kiu/lofence/pics/lofence_grafana_details.png

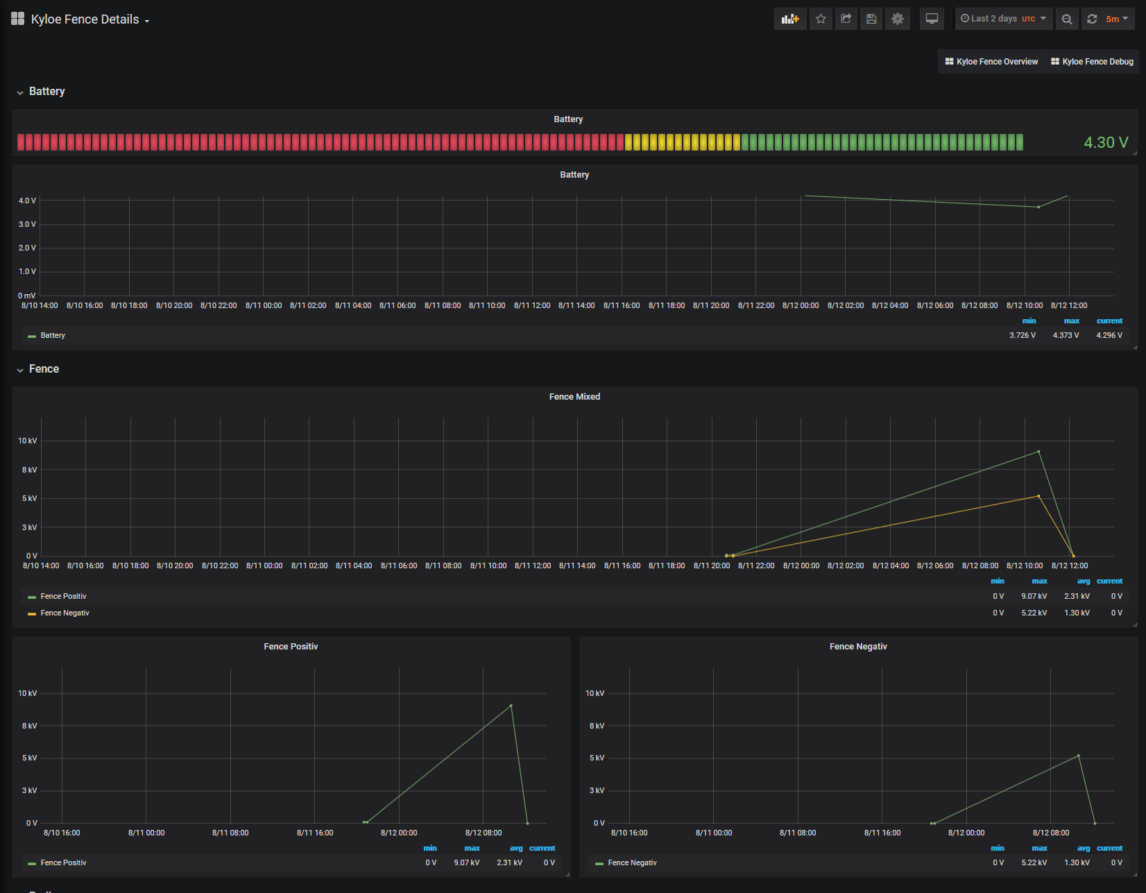
pics/lofence_grafana_details.png
