kiu/lofence/pics/lofence_rfm95_proto.jpg

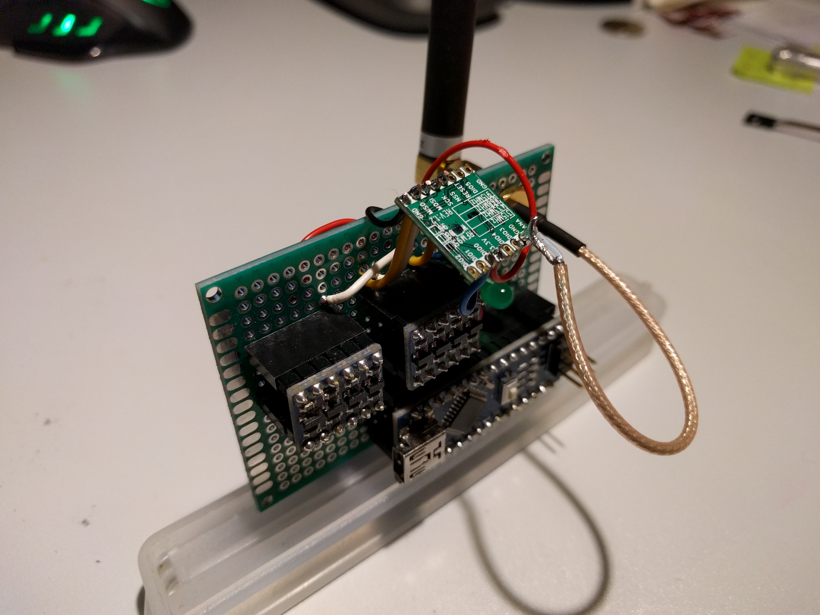
pics/lofence_rfm95_proto.jpg
