kiu/lofence/pics/lofence_ttig.jpg

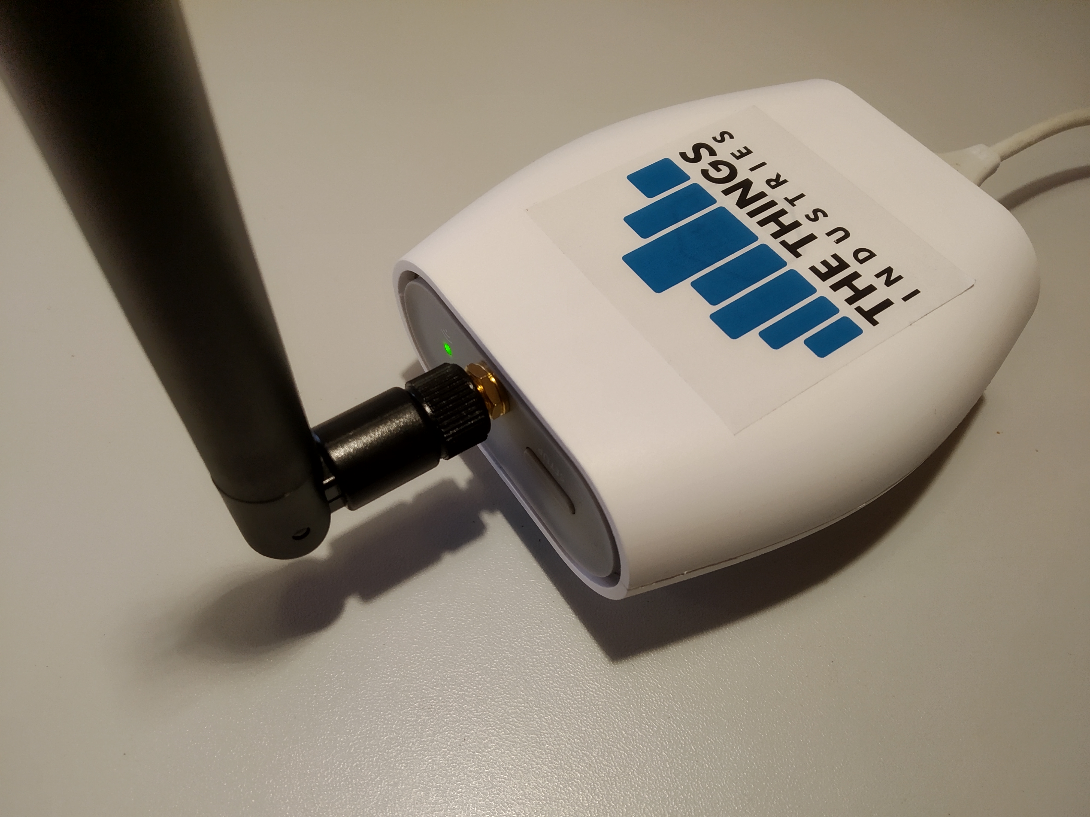
pics/lofence_ttig.jpg
