kiu/lofence/pics/lofence_mass_assembly.jpg

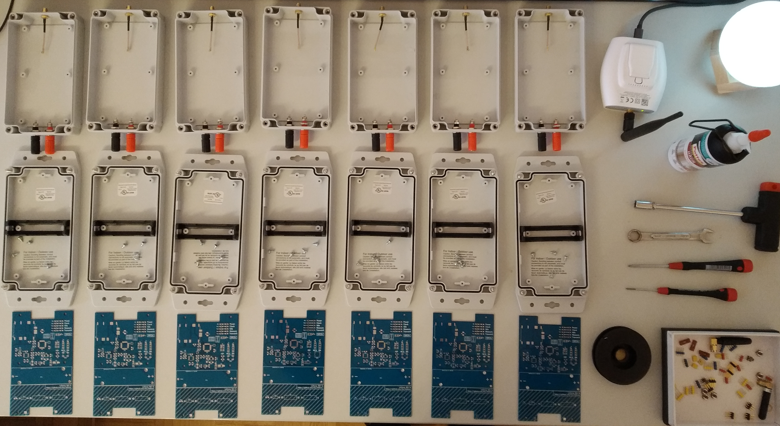
pics/lofence_mass_assembly.jpg
