kiu/lofence/pics/lofence_grafana_debug.png

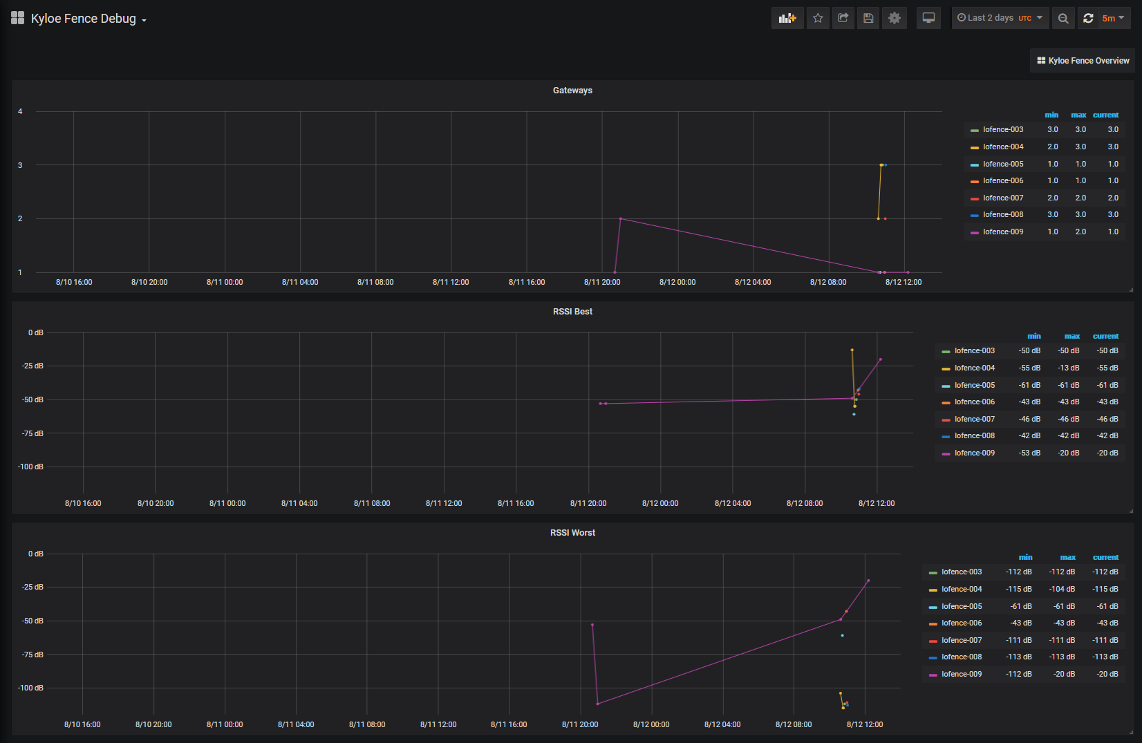
pics/lofence_grafana_debug.png
