kiu/lofence/rev_a/hardware/kicad_lofence_schema.pdf

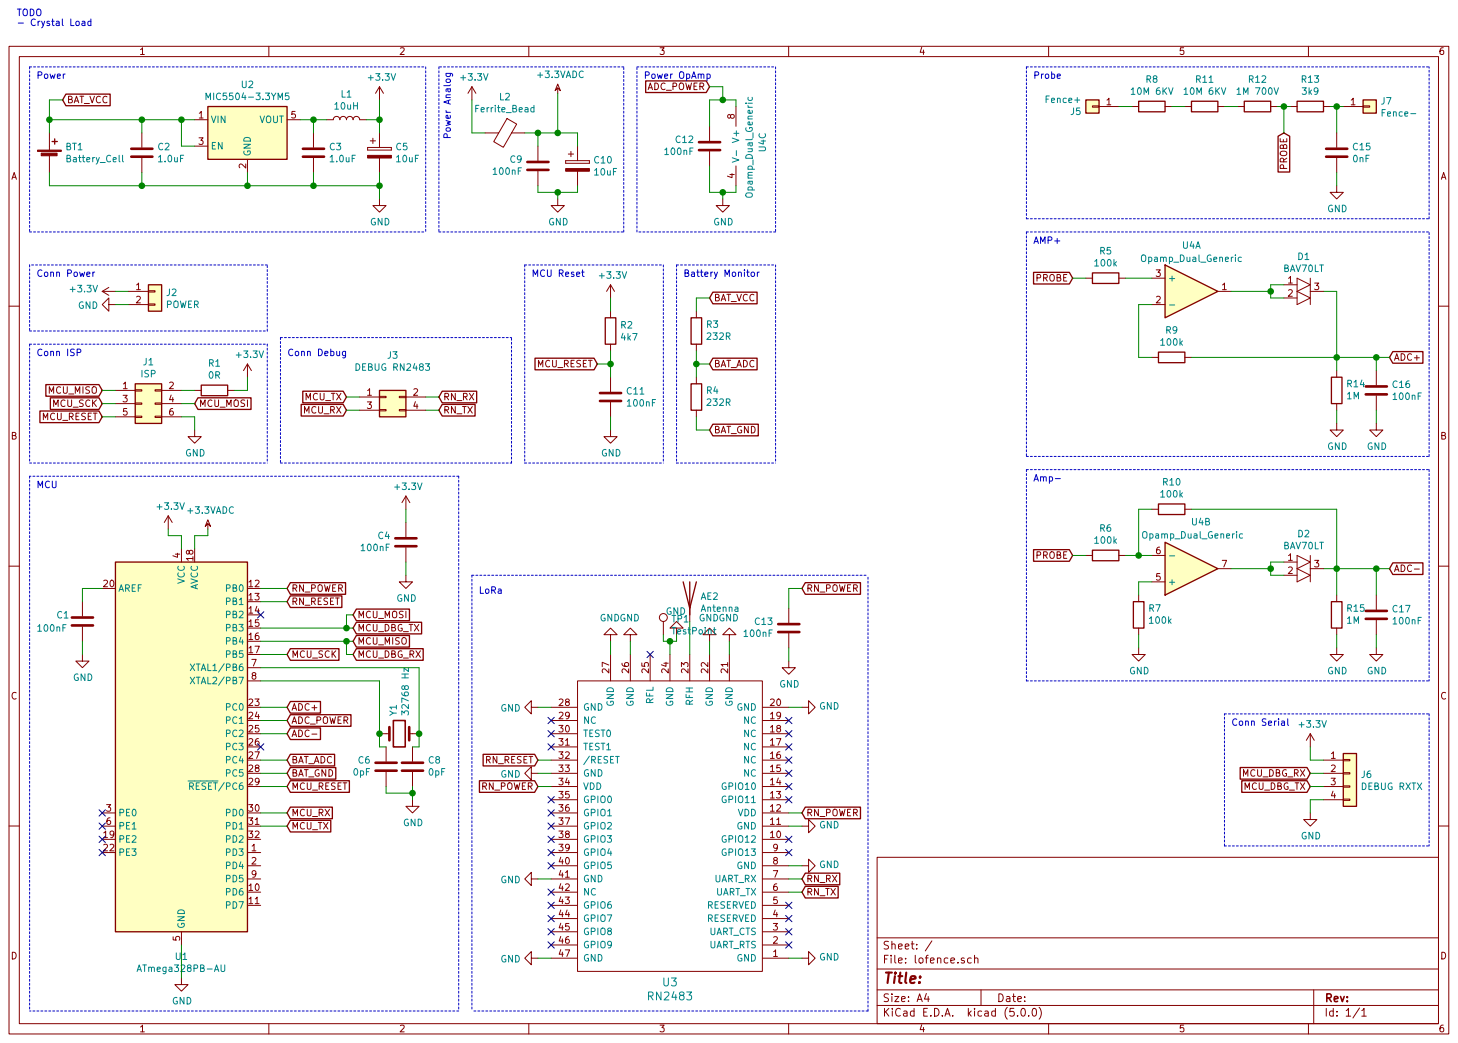
[picture p17: page 1]

ADC- ADC+ Amp- AMP+ MCU_RESET MCU Reset C9

Id: 1/1 Title: File: lofence.sch Sheet: /
