kiu/lofence/rev_a/hardware/kicad_lofence_board_bottom_mirror.pdf

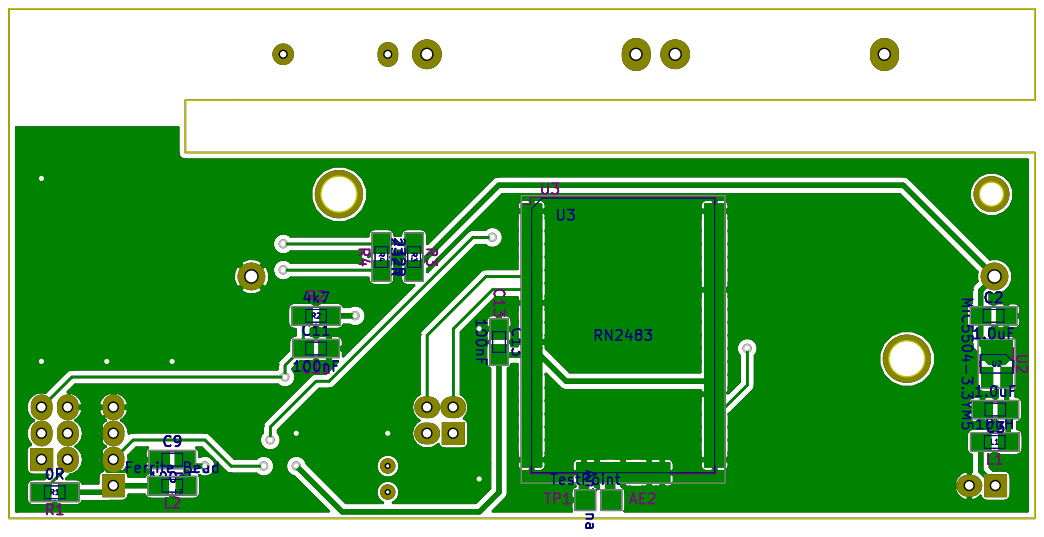
[picture p19: page 1]
