kiu/lofence/rev_a/hardware/kicad_lofence_board_front.pdf

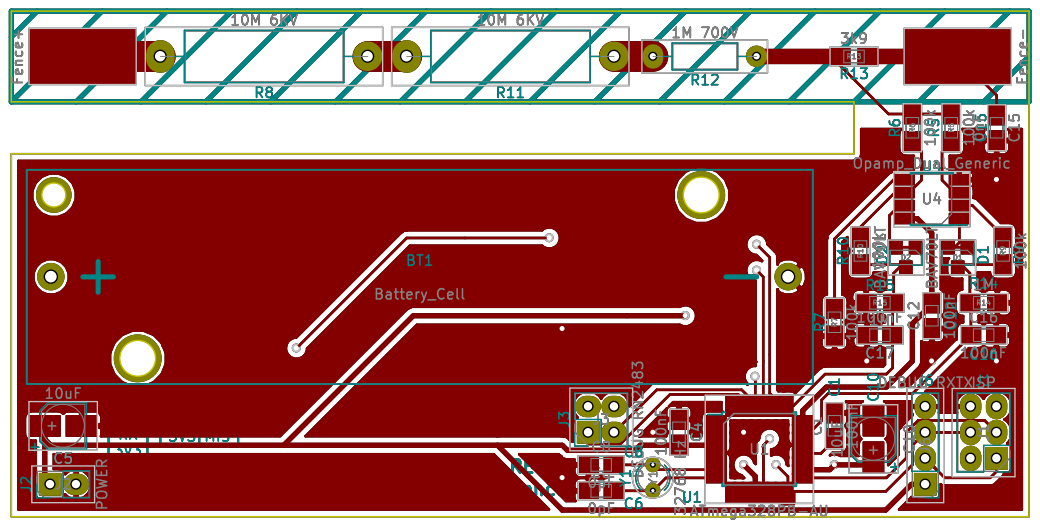
[picture p20: page 1]
