kiu/lofence/rev_b/firmware/LoFence/include/atmel_start_pins.h

/*
 * Code generated from Atmel Start.
 *
 * This file will be overwritten when reconfiguring your Atmel Start project.
 * Please copy examples or other code you want to keep to a separate file
 * to avoid losing it when reconfiguring.
 */
#ifndef ATMEL_START_PINS_H_INCLUDED
#define ATMEL_START_PINS_H_INCLUDED

#include <port.h>

/**
 * \brief Set RN_RESET pull mode
 *
 * Configure pin to pull up, down or disable pull mode, supported pull
 * modes are defined by device used
 *
 * \param[in] pull_mode Pin pull mode
 */
static inline void RN_RESET_set_pull_mode(const enum port_pull_mode pull_mode)
{
	PORTB_set_pin_pull_mode(0, pull_mode);
}

/**
 * \brief Set RN_RESET data direction
 *
 * Select if the pin data direction is input, output or disabled.
 * If disabled state is not possible, this function throws an assert.
 *
 * \param[in] direction PORT_DIR_IN  = Data direction in
 *                      PORT_DIR_OUT = Data direction out
 *                      PORT_DIR_OFF = Disables the pin
 *                      (low power state)
 */
static inline void RN_RESET_set_dir(const enum port_dir dir)
{
	PORTB_set_pin_dir(0, dir);
}

/**
 * \brief Set RN_RESET level
 *
 * Sets output level on a pin
 *
 * \param[in] level true  = Pin level set to "high" state
 *                  false = Pin level set to "low" state
 */
static inline void RN_RESET_set_level(const bool level)
{
	PORTB_set_pin_level(0, level);
}

/**
 * \brief Toggle output level on RN_RESET
 *
 * Toggle the pin level
 */
static inline void RN_RESET_toggle_level()
{
	PORTB_toggle_pin_level(0);
}

/**
 * \brief Get level on RN_RESET
 *
 * Reads the level on a pin
 */
static inline bool RN_RESET_get_level()
{
	return PORTB_get_pin_level(0);
}

/**
 * \brief Set MCU_TX pull mode
 *
 * Configure pin to pull up, down or disable pull mode, supported pull
 * modes are defined by device used
 *
 * \param[in] pull_mode Pin pull mode
 */
static inline void MCU_TX_set_pull_mode(const enum port_pull_mode pull_mode)
{
	PORTB_set_pin_pull_mode(3, pull_mode);
}

/**
 * \brief Set MCU_TX data direction
 *
 * Select if the pin data direction is input, output or disabled.
 * If disabled state is not possible, this function throws an assert.
 *
 * \param[in] direction PORT_DIR_IN  = Data direction in
 *                      PORT_DIR_OUT = Data direction out
 *                      PORT_DIR_OFF = Disables the pin
 *                      (low power state)
 */
static inline void MCU_TX_set_dir(const enum port_dir dir)
{
	PORTB_set_pin_dir(3, dir);
}

/**
 * \brief Set MCU_TX level
 *
 * Sets output level on a pin
 *
 * \param[in] level true  = Pin level set to "high" state
 *                  false = Pin level set to "low" state
 */
static inline void MCU_TX_set_level(const bool level)
{
	PORTB_set_pin_level(3, level);
}

/**
 * \brief Toggle output level on MCU_TX
 *
 * Toggle the pin level
 */
static inline void MCU_TX_toggle_level()
{
	PORTB_toggle_pin_level(3);
}

/**
 * \brief Get level on MCU_TX
 *
 * Reads the level on a pin
 */
static inline bool MCU_TX_get_level()
{
	return PORTB_get_pin_level(3);
}

/**
 * \brief Set MCU_RX pull mode
 *
 * Configure pin to pull up, down or disable pull mode, supported pull
 * modes are defined by device used
 *
 * \param[in] pull_mode Pin pull mode
 */
static inline void MCU_RX_set_pull_mode(const enum port_pull_mode pull_mode)
{
	PORTB_set_pin_pull_mode(4, pull_mode);
}

/**
 * \brief Set MCU_RX data direction
 *
 * Select if the pin data direction is input, output or disabled.
 * If disabled state is not possible, this function throws an assert.
 *
 * \param[in] direction PORT_DIR_IN  = Data direction in
 *                      PORT_DIR_OUT = Data direction out
 *                      PORT_DIR_OFF = Disables the pin
 *                      (low power state)
 */
static inline void MCU_RX_set_dir(const enum port_dir dir)
{
	PORTB_set_pin_dir(4, dir);
}

/**
 * \brief Set MCU_RX level
 *
 * Sets output level on a pin
 *
 * \param[in] level true  = Pin level set to "high" state
 *                  false = Pin level set to "low" state
 */
static inline void MCU_RX_set_level(const bool level)
{
	PORTB_set_pin_level(4, level);
}

/**
 * \brief Toggle output level on MCU_RX
 *
 * Toggle the pin level
 */
static inline void MCU_RX_toggle_level()
{
	PORTB_toggle_pin_level(4);
}

/**
 * \brief Get level on MCU_RX
 *
 * Reads the level on a pin
 */
static inline bool MCU_RX_get_level()
{
	return PORTB_get_pin_level(4);
}

/**
 * \brief Set ADC_PLUS pull mode
 *
 * Configure pin to pull up, down or disable pull mode, supported pull
 * modes are defined by device used
 *
 * \param[in] pull_mode Pin pull mode
 */
static inline void ADC_PLUS_set_pull_mode(const enum port_pull_mode pull_mode)
{
	PORTC_set_pin_pull_mode(0, pull_mode);
}

/**
 * \brief Set ADC_PLUS data direction
 *
 * Select if the pin data direction is input, output or disabled.
 * If disabled state is not possible, this function throws an assert.
 *
 * \param[in] direction PORT_DIR_IN  = Data direction in
 *                      PORT_DIR_OUT = Data direction out
 *                      PORT_DIR_OFF = Disables the pin
 *                      (low power state)
 */
static inline void ADC_PLUS_set_dir(const enum port_dir dir)
{
	PORTC_set_pin_dir(0, dir);
}

/**
 * \brief Set ADC_PLUS level
 *
 * Sets output level on a pin
 *
 * \param[in] level true  = Pin level set to "high" state
 *                  false = Pin level set to "low" state
 */
static inline void ADC_PLUS_set_level(const bool level)
{
	PORTC_set_pin_level(0, level);
}

/**
 * \brief Toggle output level on ADC_PLUS
 *
 * Toggle the pin level
 */
static inline void ADC_PLUS_toggle_level()
{
	PORTC_toggle_pin_level(0);
}

/**
 * \brief Get level on ADC_PLUS
 *
 * Reads the level on a pin
 */
static inline bool ADC_PLUS_get_level()
{
	return PORTC_get_pin_level(0);
}

/**
 * \brief Set ADC_POWER pull mode
 *
 * Configure pin to pull up, down or disable pull mode, supported pull
 * modes are defined by device used
 *
 * \param[in] pull_mode Pin pull mode
 */
static inline void ADC_POWER_set_pull_mode(const enum port_pull_mode pull_mode)
{
	PORTC_set_pin_pull_mode(1, pull_mode);
}

/**
 * \brief Set ADC_POWER data direction
 *
 * Select if the pin data direction is input, output or disabled.
 * If disabled state is not possible, this function throws an assert.
 *
 * \param[in] direction PORT_DIR_IN  = Data direction in
 *                      PORT_DIR_OUT = Data direction out
 *                      PORT_DIR_OFF = Disables the pin
 *                      (low power state)
 */
static inline void ADC_POWER_set_dir(const enum port_dir dir)
{
	PORTC_set_pin_dir(1, dir);
}

/**
 * \brief Set ADC_POWER level
 *
 * Sets output level on a pin
 *
 * \param[in] level true  = Pin level set to "high" state
 *                  false = Pin level set to "low" state
 */
static inline void ADC_POWER_set_level(const bool level)
{
	PORTC_set_pin_level(1, level);
}

/**
 * \brief Toggle output level on ADC_POWER
 *
 * Toggle the pin level
 */
static inline void ADC_POWER_toggle_level()
{
	PORTC_toggle_pin_level(1);
}

/**
 * \brief Get level on ADC_POWER
 *
 * Reads the level on a pin
 */
static inline bool ADC_POWER_get_level()
{
	return PORTC_get_pin_level(1);
}

/**
 * \brief Set ADC_MINUS pull mode
 *
 * Configure pin to pull up, down or disable pull mode, supported pull
 * modes are defined by device used
 *
 * \param[in] pull_mode Pin pull mode
 */
static inline void ADC_MINUS_set_pull_mode(const enum port_pull_mode pull_mode)
{
	PORTC_set_pin_pull_mode(2, pull_mode);
}

/**
 * \brief Set ADC_MINUS data direction
 *
 * Select if the pin data direction is input, output or disabled.
 * If disabled state is not possible, this function throws an assert.
 *
 * \param[in] direction PORT_DIR_IN  = Data direction in
 *                      PORT_DIR_OUT = Data direction out
 *                      PORT_DIR_OFF = Disables the pin
 *                      (low power state)
 */
static inline void ADC_MINUS_set_dir(const enum port_dir dir)
{
	PORTC_set_pin_dir(2, dir);
}

/**
 * \brief Set ADC_MINUS level
 *
 * Sets output level on a pin
 *
 * \param[in] level true  = Pin level set to "high" state
 *                  false = Pin level set to "low" state
 */
static inline void ADC_MINUS_set_level(const bool level)
{
	PORTC_set_pin_level(2, level);
}

/**
 * \brief Toggle output level on ADC_MINUS
 *
 * Toggle the pin level
 */
static inline void ADC_MINUS_toggle_level()
{
	PORTC_toggle_pin_level(2);
}

/**
 * \brief Get level on ADC_MINUS
 *
 * Reads the level on a pin
 */
static inline bool ADC_MINUS_get_level()
{
	return PORTC_get_pin_level(2);
}

/**
 * \brief Set BAT_ADC pull mode
 *
 * Configure pin to pull up, down or disable pull mode, supported pull
 * modes are defined by device used
 *
 * \param[in] pull_mode Pin pull mode
 */
static inline void BAT_ADC_set_pull_mode(const enum port_pull_mode pull_mode)
{
	PORTC_set_pin_pull_mode(4, pull_mode);
}

/**
 * \brief Set BAT_ADC data direction
 *
 * Select if the pin data direction is input, output or disabled.
 * If disabled state is not possible, this function throws an assert.
 *
 * \param[in] direction PORT_DIR_IN  = Data direction in
 *                      PORT_DIR_OUT = Data direction out
 *                      PORT_DIR_OFF = Disables the pin
 *                      (low power state)
 */
static inline void BAT_ADC_set_dir(const enum port_dir dir)
{
	PORTC_set_pin_dir(4, dir);
}

/**
 * \brief Set BAT_ADC level
 *
 * Sets output level on a pin
 *
 * \param[in] level true  = Pin level set to "high" state
 *                  false = Pin level set to "low" state
 */
static inline void BAT_ADC_set_level(const bool level)
{
	PORTC_set_pin_level(4, level);
}

/**
 * \brief Toggle output level on BAT_ADC
 *
 * Toggle the pin level
 */
static inline void BAT_ADC_toggle_level()
{
	PORTC_toggle_pin_level(4);
}

/**
 * \brief Get level on BAT_ADC
 *
 * Reads the level on a pin
 */
static inline bool BAT_ADC_get_level()
{
	return PORTC_get_pin_level(4);
}

/**
 * \brief Set BAT_GND pull mode
 *
 * Configure pin to pull up, down or disable pull mode, supported pull
 * modes are defined by device used
 *
 * \param[in] pull_mode Pin pull mode
 */
static inline void BAT_GND_set_pull_mode(const enum port_pull_mode pull_mode)
{
	PORTC_set_pin_pull_mode(5, pull_mode);
}

/**
 * \brief Set BAT_GND data direction
 *
 * Select if the pin data direction is input, output or disabled.
 * If disabled state is not possible, this function throws an assert.
 *
 * \param[in] direction PORT_DIR_IN  = Data direction in
 *                      PORT_DIR_OUT = Data direction out
 *                      PORT_DIR_OFF = Disables the pin
 *                      (low power state)
 */
static inline void BAT_GND_set_dir(const enum port_dir dir)
{
	PORTC_set_pin_dir(5, dir);
}

/**
 * \brief Set BAT_GND level
 *
 * Sets output level on a pin
 *
 * \param[in] level true  = Pin level set to "high" state
 *                  false = Pin level set to "low" state
 */
static inline void BAT_GND_set_level(const bool level)
{
	PORTC_set_pin_level(5, level);
}

/**
 * \brief Toggle output level on BAT_GND
 *
 * Toggle the pin level
 */
static inline void BAT_GND_toggle_level()
{
	PORTC_toggle_pin_level(5);
}

/**
 * \brief Get level on BAT_GND
 *
 * Reads the level on a pin
 */
static inline bool BAT_GND_get_level()
{
	return PORTC_get_pin_level(5);
}

/**
 * \brief Set RN_RX pull mode
 *
 * Configure pin to pull up, down or disable pull mode, supported pull
 * modes are defined by device used
 *
 * \param[in] pull_mode Pin pull mode
 */
static inline void RN_RX_set_pull_mode(const enum port_pull_mode pull_mode)
{
	PORTD_set_pin_pull_mode(0, pull_mode);
}

/**
 * \brief Set RN_RX data direction
 *
 * Select if the pin data direction is input, output or disabled.
 * If disabled state is not possible, this function throws an assert.
 *
 * \param[in] direction PORT_DIR_IN  = Data direction in
 *                      PORT_DIR_OUT = Data direction out
 *                      PORT_DIR_OFF = Disables the pin
 *                      (low power state)
 */
static inline void RN_RX_set_dir(const enum port_dir dir)
{
	PORTD_set_pin_dir(0, dir);
}

/**
 * \brief Set RN_RX level
 *
 * Sets output level on a pin
 *
 * \param[in] level true  = Pin level set to "high" state
 *                  false = Pin level set to "low" state
 */
static inline void RN_RX_set_level(const bool level)
{
	PORTD_set_pin_level(0, level);
}

/**
 * \brief Toggle output level on RN_RX
 *
 * Toggle the pin level
 */
static inline void RN_RX_toggle_level()
{
	PORTD_toggle_pin_level(0);
}

/**
 * \brief Get level on RN_RX
 *
 * Reads the level on a pin
 */
static inline bool RN_RX_get_level()
{
	return PORTD_get_pin_level(0);
}

/**
 * \brief Set RN_TX pull mode
 *
 * Configure pin to pull up, down or disable pull mode, supported pull
 * modes are defined by device used
 *
 * \param[in] pull_mode Pin pull mode
 */
static inline void RN_TX_set_pull_mode(const enum port_pull_mode pull_mode)
{
	PORTD_set_pin_pull_mode(1, pull_mode);
}

/**
 * \brief Set RN_TX data direction
 *
 * Select if the pin data direction is input, output or disabled.
 * If disabled state is not possible, this function throws an assert.
 *
 * \param[in] direction PORT_DIR_IN  = Data direction in
 *                      PORT_DIR_OUT = Data direction out
 *                      PORT_DIR_OFF = Disables the pin
 *                      (low power state)
 */
static inline void RN_TX_set_dir(const enum port_dir dir)
{
	PORTD_set_pin_dir(1, dir);
}

/**
 * \brief Set RN_TX level
 *
 * Sets output level on a pin
 *
 * \param[in] level true  = Pin level set to "high" state
 *                  false = Pin level set to "low" state
 */
static inline void RN_TX_set_level(const bool level)
{
	PORTD_set_pin_level(1, level);
}

/**
 * \brief Toggle output level on RN_TX
 *
 * Toggle the pin level
 */
static inline void RN_TX_toggle_level()
{
	PORTD_toggle_pin_level(1);
}

/**
 * \brief Get level on RN_TX
 *
 * Reads the level on a pin
 */
static inline bool RN_TX_get_level()
{
	return PORTD_get_pin_level(1);
}

/**
 * \brief Set LED_CLK pull mode
 *
 * Configure pin to pull up, down or disable pull mode, supported pull
 * modes are defined by device used
 *
 * \param[in] pull_mode Pin pull mode
 */
static inline void LED_CLK_set_pull_mode(const enum port_pull_mode pull_mode)
{
	PORTE_set_pin_pull_mode(0, pull_mode);
}

/**
 * \brief Set LED_CLK data direction
 *
 * Select if the pin data direction is input, output or disabled.
 * If disabled state is not possible, this function throws an assert.
 *
 * \param[in] direction PORT_DIR_IN  = Data direction in
 *                      PORT_DIR_OUT = Data direction out
 *                      PORT_DIR_OFF = Disables the pin
 *                      (low power state)
 */
static inline void LED_CLK_set_dir(const enum port_dir dir)
{
	PORTE_set_pin_dir(0, dir);
}

/**
 * \brief Set LED_CLK level
 *
 * Sets output level on a pin
 *
 * \param[in] level true  = Pin level set to "high" state
 *                  false = Pin level set to "low" state
 */
static inline void LED_CLK_set_level(const bool level)
{
	PORTE_set_pin_level(0, level);
}

/**
 * \brief Toggle output level on LED_CLK
 *
 * Toggle the pin level
 */
static inline void LED_CLK_toggle_level()
{
	PORTE_toggle_pin_level(0);
}

/**
 * \brief Get level on LED_CLK
 *
 * Reads the level on a pin
 */
static inline bool LED_CLK_get_level()
{
	return PORTE_get_pin_level(0);
}

/**
 * \brief Set LED_IDLE pull mode
 *
 * Configure pin to pull up, down or disable pull mode, supported pull
 * modes are defined by device used
 *
 * \param[in] pull_mode Pin pull mode
 */
static inline void LED_IDLE_set_pull_mode(const enum port_pull_mode pull_mode)
{
	PORTE_set_pin_pull_mode(1, pull_mode);
}

/**
 * \brief Set LED_IDLE data direction
 *
 * Select if the pin data direction is input, output or disabled.
 * If disabled state is not possible, this function throws an assert.
 *
 * \param[in] direction PORT_DIR_IN  = Data direction in
 *                      PORT_DIR_OUT = Data direction out
 *                      PORT_DIR_OFF = Disables the pin
 *                      (low power state)
 */
static inline void LED_IDLE_set_dir(const enum port_dir dir)
{
	PORTE_set_pin_dir(1, dir);
}

/**
 * \brief Set LED_IDLE level
 *
 * Sets output level on a pin
 *
 * \param[in] level true  = Pin level set to "high" state
 *                  false = Pin level set to "low" state
 */
static inline void LED_IDLE_set_level(const bool level)
{
	PORTE_set_pin_level(1, level);
}

/**
 * \brief Toggle output level on LED_IDLE
 *
 * Toggle the pin level
 */
static inline void LED_IDLE_toggle_level()
{
	PORTE_toggle_pin_level(1);
}

/**
 * \brief Get level on LED_IDLE
 *
 * Reads the level on a pin
 */
static inline bool LED_IDLE_get_level()
{
	return PORTE_get_pin_level(1);
}

/**
 * \brief Set LED_MSR pull mode
 *
 * Configure pin to pull up, down or disable pull mode, supported pull
 * modes are defined by device used
 *
 * \param[in] pull_mode Pin pull mode
 */
static inline void LED_MSR_set_pull_mode(const enum port_pull_mode pull_mode)
{
	PORTE_set_pin_pull_mode(2, pull_mode);
}

/**
 * \brief Set LED_MSR data direction
 *
 * Select if the pin data direction is input, output or disabled.
 * If disabled state is not possible, this function throws an assert.
 *
 * \param[in] direction PORT_DIR_IN  = Data direction in
 *                      PORT_DIR_OUT = Data direction out
 *                      PORT_DIR_OFF = Disables the pin
 *                      (low power state)
 */
static inline void LED_MSR_set_dir(const enum port_dir dir)
{
	PORTE_set_pin_dir(2, dir);
}

/**
 * \brief Set LED_MSR level
 *
 * Sets output level on a pin
 *
 * \param[in] level true  = Pin level set to "high" state
 *                  false = Pin level set to "low" state
 */
static inline void LED_MSR_set_level(const bool level)
{
	PORTE_set_pin_level(2, level);
}

/**
 * \brief Toggle output level on LED_MSR
 *
 * Toggle the pin level
 */
static inline void LED_MSR_toggle_level()
{
	PORTE_toggle_pin_level(2);
}

/**
 * \brief Get level on LED_MSR
 *
 * Reads the level on a pin
 */
static inline bool LED_MSR_get_level()
{
	return PORTE_get_pin_level(2);
}

/**
 * \brief Set LED_TX pull mode
 *
 * Configure pin to pull up, down or disable pull mode, supported pull
 * modes are defined by device used
 *
 * \param[in] pull_mode Pin pull mode
 */
static inline void LED_TX_set_pull_mode(const enum port_pull_mode pull_mode)
{
	PORTE_set_pin_pull_mode(3, pull_mode);
}

/**
 * \brief Set LED_TX data direction
 *
 * Select if the pin data direction is input, output or disabled.
 * If disabled state is not possible, this function throws an assert.
 *
 * \param[in] direction PORT_DIR_IN  = Data direction in
 *                      PORT_DIR_OUT = Data direction out
 *                      PORT_DIR_OFF = Disables the pin
 *                      (low power state)
 */
static inline void LED_TX_set_dir(const enum port_dir dir)
{
	PORTE_set_pin_dir(3, dir);
}

/**
 * \brief Set LED_TX level
 *
 * Sets output level on a pin
 *
 * \param[in] level true  = Pin level set to "high" state
 *                  false = Pin level set to "low" state
 */
static inline void LED_TX_set_level(const bool level)
{
	PORTE_set_pin_level(3, level);
}

/**
 * \brief Toggle output level on LED_TX
 *
 * Toggle the pin level
 */
static inline void LED_TX_toggle_level()
{
	PORTE_toggle_pin_level(3);
}

/**
 * \brief Get level on LED_TX
 *
 * Reads the level on a pin
 */
static inline bool LED_TX_get_level()
{
	return PORTE_get_pin_level(3);
}

#endif /* ATMEL_START_PINS_H_INCLUDED */
